Sylvia3366/drs-pad/case/Bottom case/bottom1.png

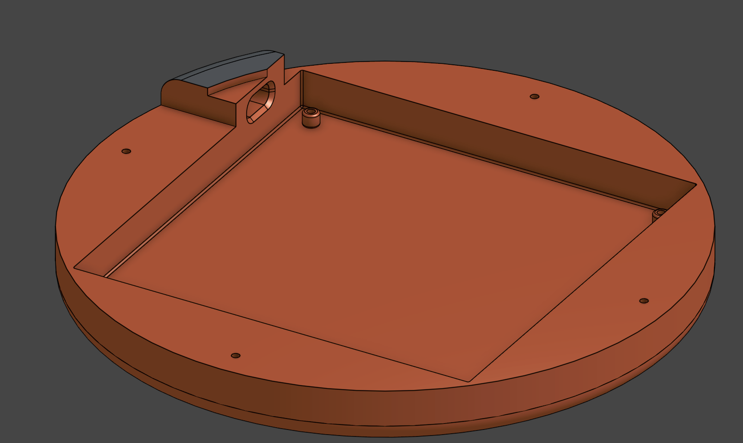
case/Bottom case/bottom1.png
