Sylvia3366/drs-pad/case/Bottom case/bottom.png

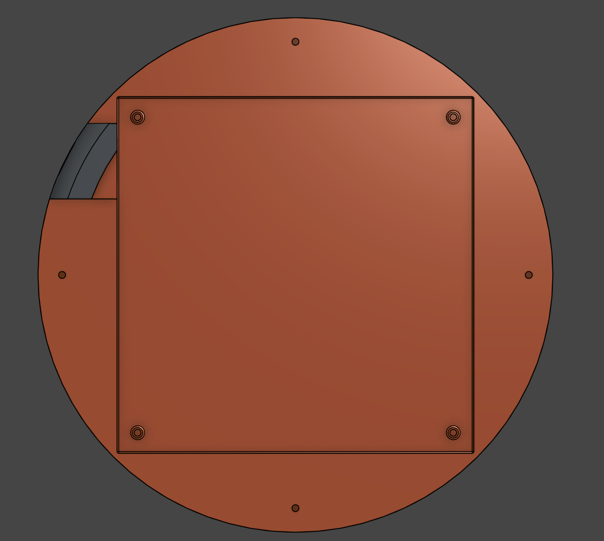
case/Bottom case/bottom.png
