Sylvia3366/drs-pad/case/CAD/1.14" IPS LCD/1.14"_ips_lcd.png

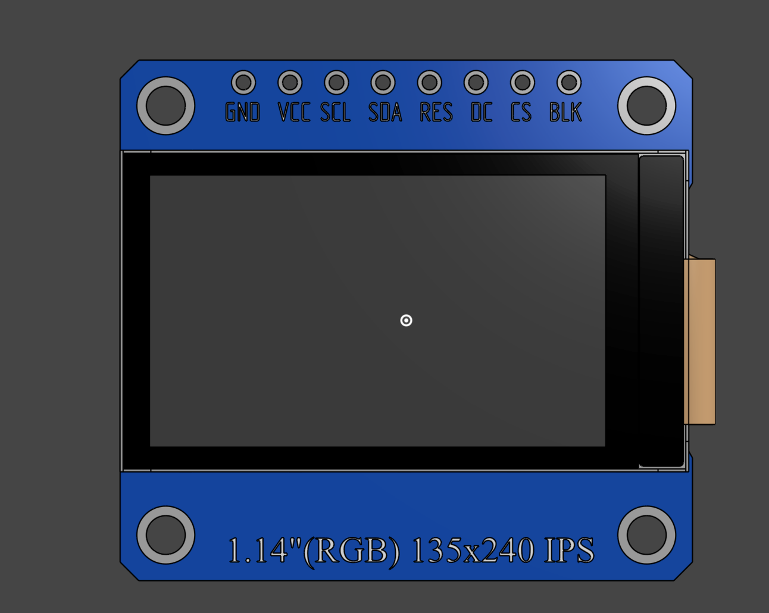
case/CAD/1.14" IPS LCD/1.14"_ips_lcd.png
