Sylvia3366/drs-pad/case/CAD/1N4148 Diode (SOD-123)/diode_sod123.png

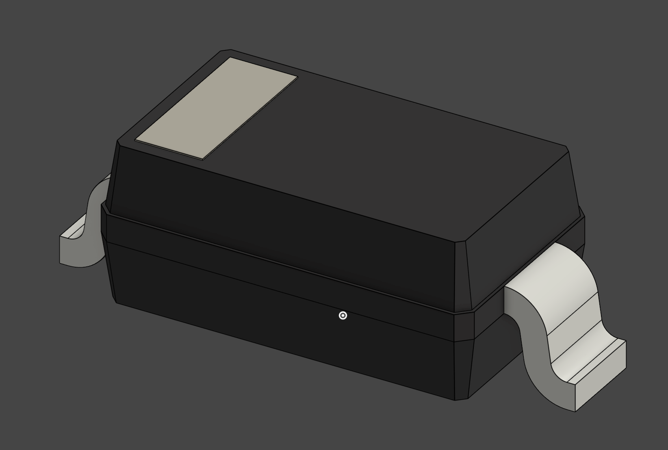
case/CAD/1N4148 Diode (SOD-123)/diode_sod123.png
