Sylvia3366/drs-pad/case/CAD/M2 4mm Screw/M2_4mm.png

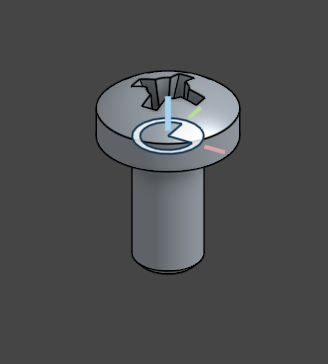
case/CAD/M2 4mm Screw/M2_4mm.png
