Sylvia3366/drs-pad/case/Top case/top.png

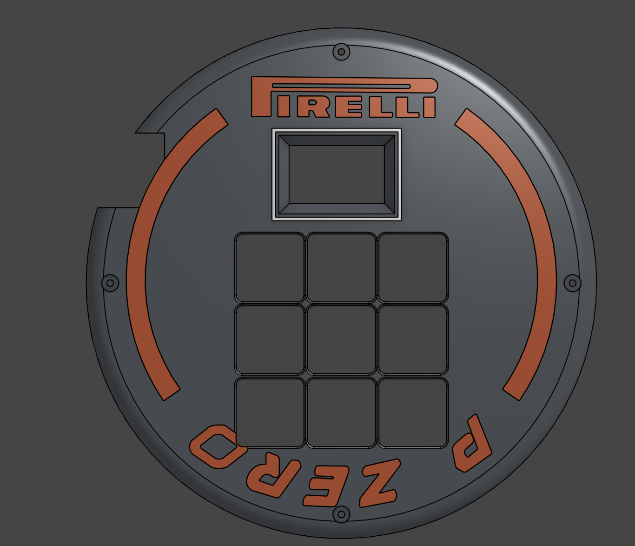
case/Top case/top.png
